Dachtire/fercus/firmware/keyboard/ch32v20x/ble/profile/hiddev.c

/********************************** (C) COPYRIGHT *******************************
 * File Name          : hiddev.c
 * Author             : WCH
 * Version            : V1.0
 * Date               : 2018/12/10
 * Description        : HID device task handler
 *********************************************************************************
 * Copyright (c) 2021 Nanjing Qinheng Microelectronics Co., Ltd.
 * Attention: This software (modified or not) and binary are used for 
 * microcontroller manufactured by Nanjing Qinheng Microelectronics.
 *******************************************************************************/

/*********************************************************************
 * INCLUDES
 */

#include "hiddev.h"
#include "battservice.h"
#include "ble-hid-keyboard.h"
#include "config.h"
#include "devinfoservice.h"
#include "scanparamservice.h"

/*********************************************************************
 * MACROS
 */

// Battery measurement period in (625us)
#define DEFAULT_BATT_PERIOD               15000

// TRUE to run scan parameters refresh notify test
#define DEFAULT_SCAN_PARAM_NOTIFY_TEST    TRUE

// Advertising intervals (units of 625us, 160=100ms)
#define HID_INITIAL_ADV_INT_MIN           48
#define HID_INITIAL_ADV_INT_MAX           80
#define HID_HIGH_ADV_INT_MIN              32
#define HID_HIGH_ADV_INT_MAX              48
#define HID_LOW_ADV_INT_MIN               160
#define HID_LOW_ADV_INT_MAX               160

// Advertising timeouts in sec
#define HID_INITIAL_ADV_TIMEOUT           60
#define HID_HIGH_ADV_TIMEOUT              5
#define HID_LOW_ADV_TIMEOUT               0

// Heart Rate Task Events
#define START_DEVICE_EVT                  0x0001
#define BATT_PERIODIC_EVT                 0x0002

/*********************************************************************
 * CONSTANTS
 */

/*********************************************************************
 * TYPEDEFS
 */

/*********************************************************************
 * GLOBAL VARIABLES
 */

// Task ID
uint8_t hidDevTaskId;

/*********************************************************************
 * EXTERNAL VARIABLES
 */

/*********************************************************************
 * EXTERNAL FUNCTIONS
 */

/*********************************************************************
 * LOCAL VARIABLES
 */

// GAP State
static gapRole_States_t hidDevGapState = GAPROLE_INIT;

// TRUE if connection is secure
static uint8_t hidDevConnSecure = FALSE;

// GAP connection handle
static uint16_t gapConnHandle;

// Status of last pairing
static uint8_t pairingStatus = SUCCESS;

static hidRptMap_t *pHidDevRptTbl;

static uint8_t hidDevRptTblLen;

static hidDevCB_t *pHidDevCB;

static hidDevCfg_t *pHidDevCfg;

/*********************************************************************
 * LOCAL FUNCTIONS
 */

static void hidDev_ProcessTMOSMsg(tmos_event_hdr_t *pMsg);
static void hidDevProcessGattMsg(gattMsgEvent_t *pMsg);
static void hidDevProcessGAPMsg(gapRoleEvent_t *pEvent);
static void hidDevDisconnected(void);
static void hidDevGapStateCB(gapRole_States_t newState, gapRoleEvent_t *pEvent);
static void hidDevParamUpdateCB(uint16_t connHandle, uint16_t connInterval,
                                uint16_t connSlaveLatency, uint16_t connTimeout);
static void hidDevPairStateCB(uint16_t connHandle, uint8_t state, uint8_t status);
static void hidDevPasscodeCB(uint8_t *deviceAddr, uint16_t connectionHandle,
                             uint8_t uiInputs, uint8_t uiOutputs);
static void hidDevBattCB(uint8_t event);
static void hidDevScanParamCB(uint8_t event);
static void hidDevBattPeriodicTask(void);

static hidRptMap_t *hidDevRptByHandle(uint16_t handle);
static hidRptMap_t *hidDevRptById(uint8_t id, uint8_t type);
static hidRptMap_t *hidDevRptByCccdHandle(uint16_t handle);

static uint8_t hidDevSendReport(uint8_t id, uint8_t type, uint8_t len, uint8_t *pData);
static void    hidDevHighAdvertising(void);
static void    hidDevLowAdvertising(void);
static void    hidDevInitialAdvertising(void);
static uint8_t hidDevBondCount(void);
static uint8_t HidDev_sendNoti(uint16_t handle, uint8_t len, uint8_t *pData);
/*********************************************************************
 * PROFILE CALLBACKS
 */

// GAP Role Callbacks
static gapRolesCBs_t hidDev_PeripheralCBs = {
    hidDevGapStateCB, // Profile State Change Callbacks
    NULL,             // When a valid RSSI is read from controller
    hidDevParamUpdateCB
};

// Bond Manager Callbacks
static gapBondCBs_t hidDevBondCB = {
    hidDevPasscodeCB,
    hidDevPairStateCB,
    NULL  // oob callback
};

/*********************************************************************
 * PUBLIC FUNCTIONS
 */

/*********************************************************************
 * @fn      HidDev_Init
 *
 * @brief   Initialization function for the Hid Dev Task.
 *          This is called during initialization and should contain
 *          any application specific initialization (ie. hardware
 *          initialization/setup, table initialization, power up
 *          notificaiton ... ).
 *
 * @param   task_id - the ID assigned by TMOS.  This ID should be
 *                    used to send messages and set timers.
 *
 * @return  none
 */
void HidDev_Init()
{
    hidDevTaskId = TMOS_ProcessEventRegister(HidDev_ProcessEvent);

    // Setup the GAP Bond Manager
    {
        uint8_t syncWL = TRUE;

        // If a bond is created, the HID Device should write the address of the
        // HID Host in the HID Device controller's white list and set the HID
        // Device controller's advertising filter policy to 'process scan and
        // connection requests only from devices in the White List'.
        GAPBondMgr_SetParameter(GAPBOND_AUTO_SYNC_WL, sizeof(uint8_t), &syncWL);
    }

    // Set up services
    GGS_AddService(GATT_ALL_SERVICES);         // GAP
    GATTServApp_AddService(GATT_ALL_SERVICES); // GATT attributes
    DevInfo_AddService();
    Batt_AddService();
    ScanParam_AddService();

    // Register for Battery service callback
    Batt_Register(hidDevBattCB);

    // Register for Scan Parameters service callback
    ScanParam_Register(hidDevScanParamCB);

    // Setup a delayed profile startup
    tmos_set_event(hidDevTaskId, START_DEVICE_EVT);
}

/*********************************************************************
 * @fn      HidDev_ProcessEvent
 *
 * @brief   Hid Dev Task event processor.  This function
 *          is called to process all events for the task.  Events
 *          include timers, messages and any other user defined events.
 *
 * @param   task_id  - The TMOS assigned task ID.
 * @param   events - events to process.  This is a bit map and can
 *                   contain more than one event.
 *
 * @return  events not processed
 */
uint16_t HidDev_ProcessEvent(uint8_t task_id, uint16_t events)
{
    //VOID task_id; // TMOS required parameter that isn't used in this function

    if(events & SYS_EVENT_MSG)
    {
        uint8_t *pMsg;

        if((pMsg = tmos_msg_receive(hidDevTaskId)) != NULL)
        {
            hidDev_ProcessTMOSMsg((tmos_event_hdr_t *)pMsg);

            // Release the TMOS message
            tmos_msg_deallocate(pMsg);
        }

        // return unprocessed events
        return (events ^ SYS_EVENT_MSG);
    }

    if(events & START_DEVICE_EVT)
    {
        // Start the Device
        GAPRole_PeripheralStartDevice(hidDevTaskId, &hidDevBondCB, &hidDev_PeripheralCBs);

        return (events ^ START_DEVICE_EVT);
    }

    if(events & BATT_PERIODIC_EVT)
    {
        // Perform periodic battery task
        hidDevBattPeriodicTask();

        return (events ^ BATT_PERIODIC_EVT);
    }

    return 0;
}

/*********************************************************************
 * @fn      HidDev_Register
 *
 * @brief   Register a callback function with HID Dev.
 *
 * @param   pCfg - Parameter configuration.
 * @param   pfnServiceCB - Callback function.
 *
 * @return  None.
 */
void HidDev_Register(hidDevCfg_t *pCfg, hidDevCB_t *pCBs)
{
    pHidDevCB = pCBs;
    pHidDevCfg = pCfg;
}

/*********************************************************************
 * @fn      HidDev_RegisterReports
 *
 * @brief   Register the report table with HID Dev.
 *
 * @param   numReports - Length of report table.
 * @param   pRpt - Report table.
 *
 * @return  None.
 */
void HidDev_RegisterReports(uint8_t numReports, hidRptMap_t *pRpt)
{
    pHidDevRptTbl = pRpt;
    hidDevRptTblLen = numReports;
}

/*********************************************************************
 * @fn      HidDev_Report
 *
 * @brief   Send a HID report.
 *
 * @param   id - HID report ID.
 * @param   type - HID report type.
 * @param   len - Length of report.
 * @param   pData - Report data.
 *
 * @return  None.
 */
uint8_t HidDev_Report(uint8_t id, uint8_t type, uint8_t len, uint8_t *pData)
{
    // if connected
    if(hidDevGapState == GAPROLE_CONNECTED)
    {
        // if connection is secure
        if(hidDevConnSecure)
        {
            // send report
            return hidDevSendReport(id, type, len, pData);
        }
    }
    // else if not already advertising
    else if(hidDevGapState != GAPROLE_ADVERTISING)
    {
        // if bonded
        if(hidDevBondCount() > 0)
        {
            // start high duty cycle advertising
            hidDevHighAdvertising();
        }
        // else not bonded
        else
        {
            // start initial advertising
            hidDevInitialAdvertising();
        }
    }
    return bleNotReady;
}

/*********************************************************************
 * @fn      HidDev_Close
 *
 * @brief   Close the connection or stop advertising.
 *
 * @return  None.
 */
void HidDev_Close(void)
{
    uint8_t param;

    // if connected then disconnect
    if(hidDevGapState == GAPROLE_CONNECTED)
    {
        GAPRole_TerminateLink(gapConnHandle);
    }
    // else stop advertising
    else
    {
        param = FALSE;
        GAPRole_SetParameter(GAPROLE_ADVERT_ENABLED, sizeof(uint8_t), &param);
    }
}

/*********************************************************************
 * @fn      HidDev_SetParameter
 *
 * @brief   Set a HID Dev parameter.
 *
 * @param   param - Profile parameter ID
 * @param   len - length of data to right
 * @param   pValue - pointer to data to write.  This is dependent on
 *          the parameter ID and WILL be cast to the appropriate
 *          data type (example: data type of uint16_t will be cast to
 *          uint16_t pointer).
 *
 * @return  bStatus_t
 */
bStatus_t HidDev_SetParameter(uint8_t param, uint8_t len, void *pValue)
{
    bStatus_t ret = SUCCESS;

    switch(param)
    {
        case HIDDEV_ERASE_ALLBONDS:
            if(len == 0)
            {
                // Drop connection
                if(hidDevGapState == GAPROLE_CONNECTED)
                {
                    GAPRole_TerminateLink(gapConnHandle);
                }

                // Erase bonding info
                GAPBondMgr_SetParameter(GAPBOND_ERASE_ALLBONDS, 0, NULL);
            }
            else
            {
                ret = bleInvalidRange;
            }
            break;

        default:
            ret = INVALIDPARAMETER;
            break;
    }

    return (ret);
}
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
